IDMIL/PedalMotorController/src/MotorInfo/MotorInfo.h

#pragma once

#include <AccelStepper.h>
#include <SerialSensorGyro.h>

#include <Menu.h>
#include <AxisSelectMenu.h>
#include <CurveSelectMenu.h>
#include <MultiplierSelectMenu.h>
#include <StepperAngleMenu.h>
#include <StepperPositionMenu.h>

#include <LiquidCrystal.h>

/**
 * MotorInfo: A class for encapsulating PMC motor behavior & state
 * @author Ian Doherty
 */
class MotorInfo {
    public:
        enum class Axis {
            X = 0,
            Y = 1,
            Z = 2
        };

        enum class Curve {
            LINEAR = 0,
            EXPONENTIAL = 1,
            LOGARITHMIC = 2,
            QUADRATIC = 3
        };

        MotorInfo(int motorNum, AccelStepper stepper, long maxSteps, SerialSensorGyro* ssg, LiquidCrystal* lcd, Joystick* joystick);
        
        /**
         * Moves the motor based on the object's state.
         */
        void run();

        int motorNum;

        AccelStepper stepper;
        long currentStep = 0;
        long maxSteps;

        long multiplier = 10000;
        Axis axis = Axis::X;
        Curve curve = Curve::LINEAR;

        SerialSensorGyro* ssg;
        LiquidCrystal* lcd;
        Joystick* joystick;

        StepperPositionMenu stepperPositionMenu;
        StepperAngleMenu stepperAngleMenu;
        AxisSelectMenu axisSelectMenu;
        MultiplierSelectMenu multiplierSelectMenu;
        CurveSelectMenu curveSelectMenu;

        Menu* menus[5];
};
